martamusikmaschine/mmm/3d/led_ring.jpg

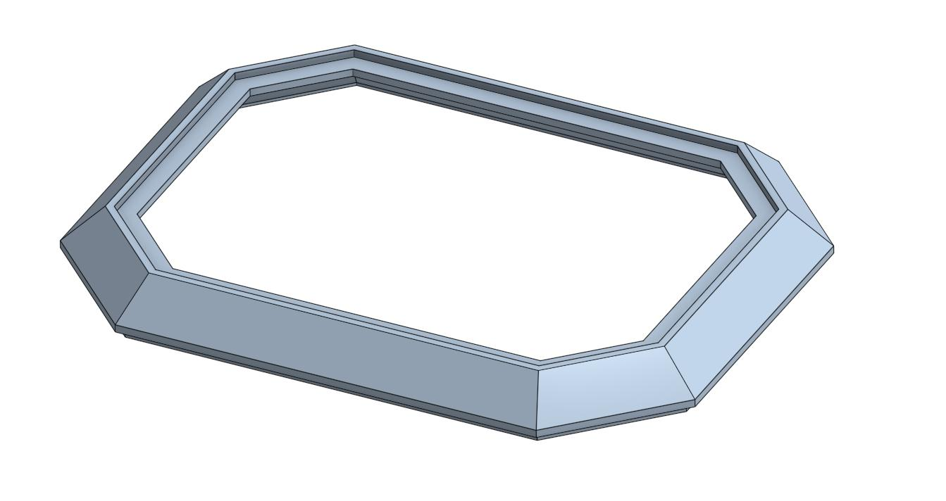
3d/led_ring.jpg
