martamusikmaschine/mmm/3d/rfid_reader_main.jpg

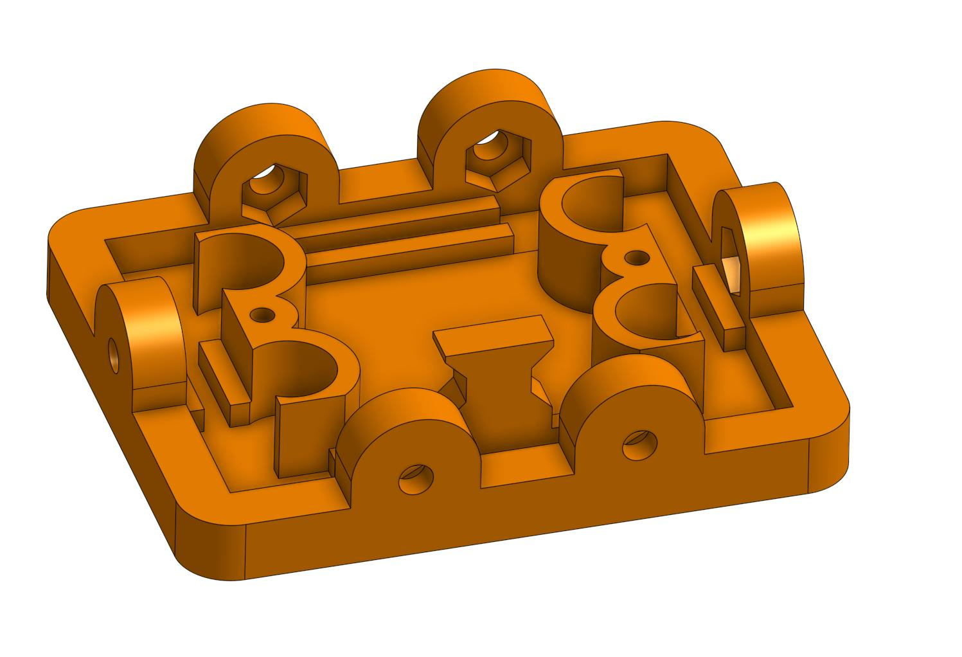
3d/rfid_reader_main.jpg
