martamusikmaschine/mmm/3d/rfid_tag_44_29_cap.jpg

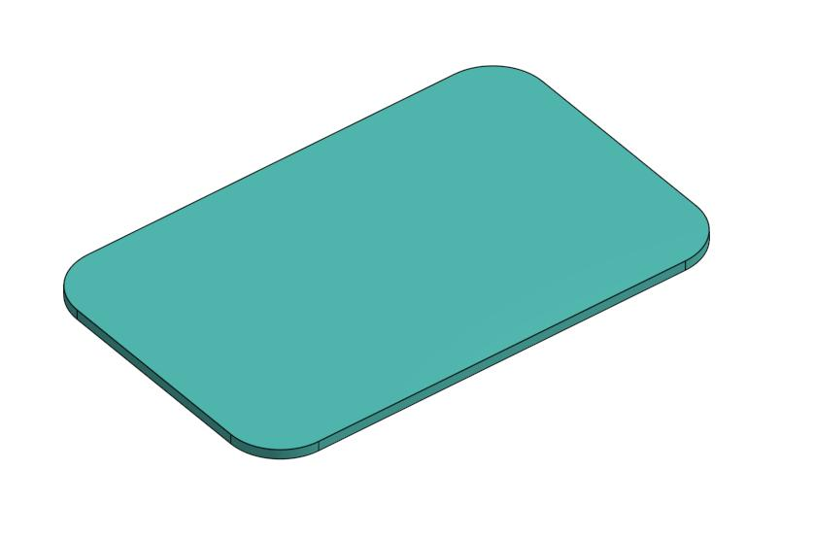
3d/rfid_tag_44_29_cap.jpg
