martamusikmaschine/mmm/3d/top_plate.jpg

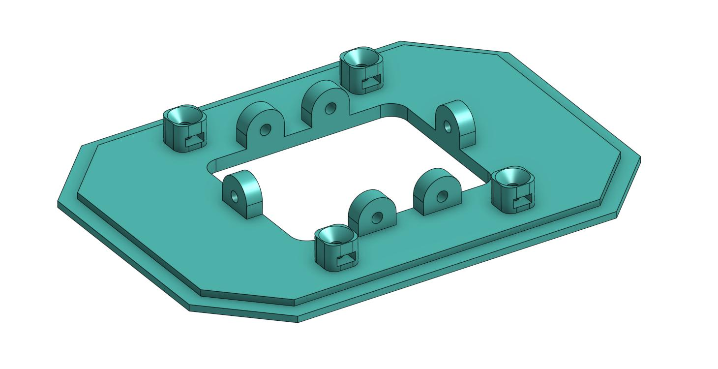
3d/top_plate.jpg
