martamusikmaschine/mmm/3d/rfid_tag_44_29_photo_holder.stl

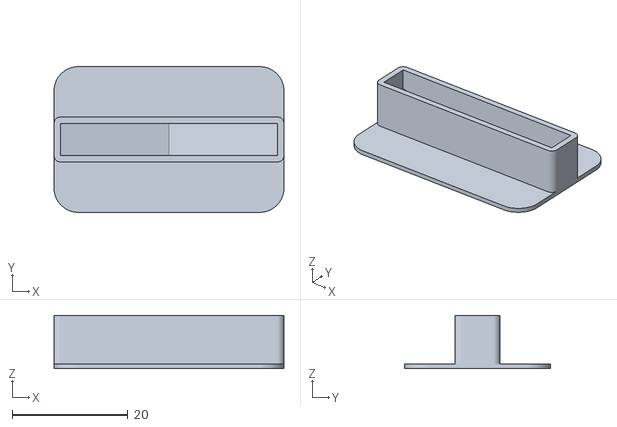
[picture p25: CAD file, 2019-08-26]
3d/rfid_tag_44_29_photo_holder.stl
39.8 x 25.2 x 9.20
