martamusikmaschine/mmm/3d/rfid_tag_50_30_base.stl

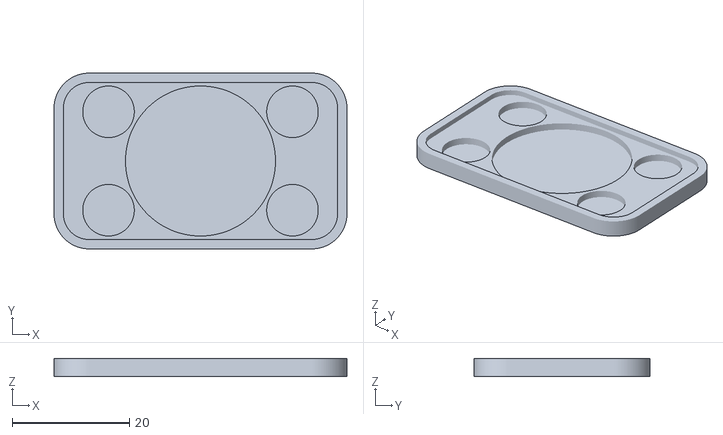
[picture p26: CAD file, 2019-08-26]
3d/rfid_tag_50_30_base.stl
50.0 x 30.0 x 3.10
