martamusikmaschine/mmm/3d/rfid_tag_80_30_cap.stl

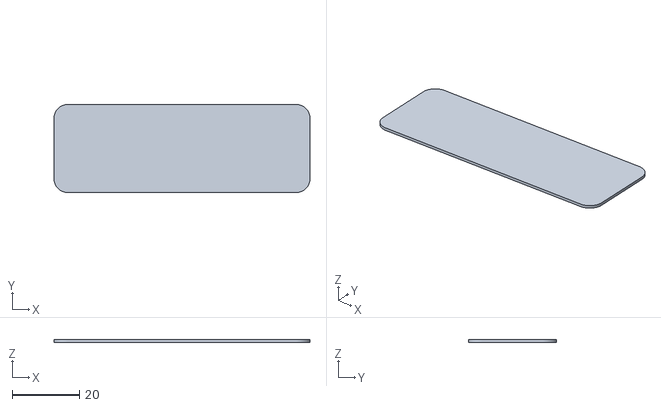
[picture p27: CAD file, 2019-08-26]
3d/rfid_tag_80_30_cap.stl
76.2 x 26.2 x 0.8
