martamusikmaschine/mmm/3d/rfid_tag_62_32_base.stl

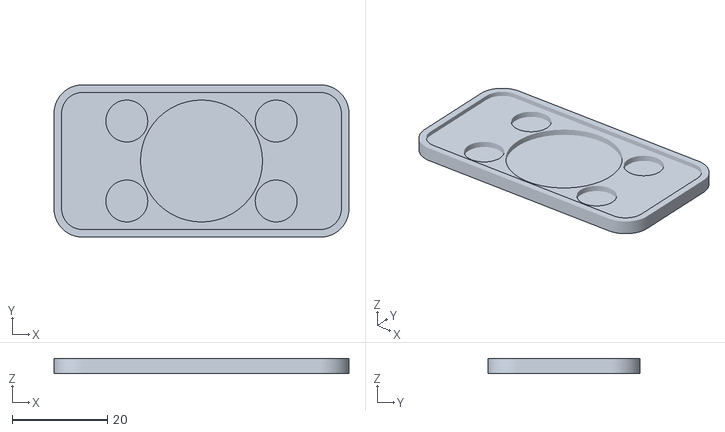
[picture p28: CAD file, 2019-08-26]
3d/rfid_tag_62_32_base.stl
62.0 x 32.0 x 3.10
