martamusikmaschine/mmm/3d/rfid_tag_50_30_cap.stl

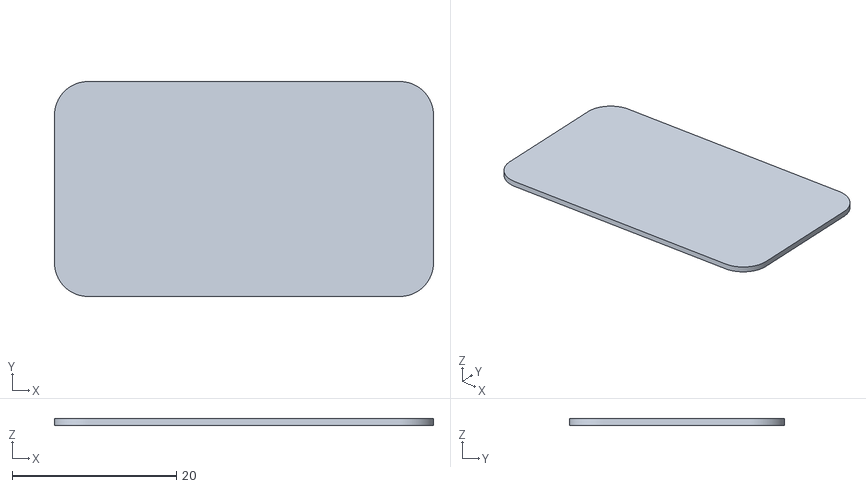
[picture p29: CAD file, 2019-08-26]
3d/rfid_tag_50_30_cap.stl
46.2 x 26.2 x 0.8
