martamusikmaschine/mmm/3d/rfid_tag_80_30_base.stl

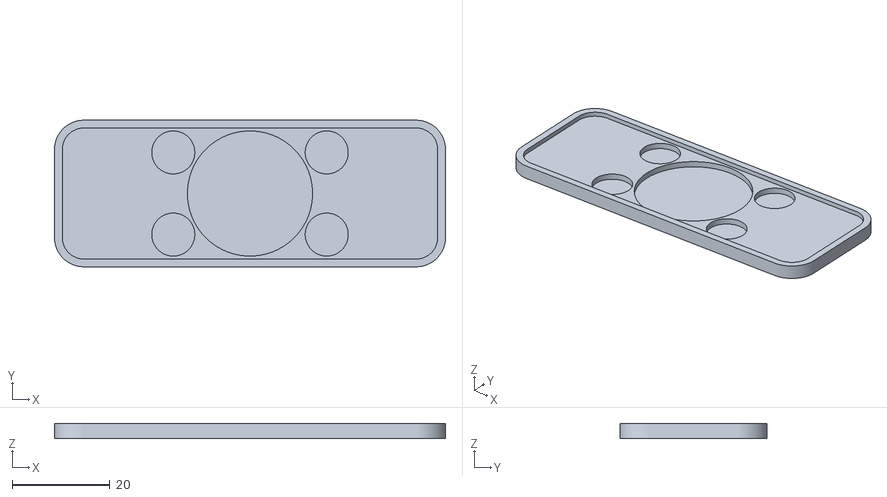
[picture p30: CAD file, 2019-08-26]
3d/rfid_tag_80_30_base.stl
80.0 x 30.0 x 3.10
