martamusikmaschine/mmm/3d/rfid_tag_62_32_cap.stl

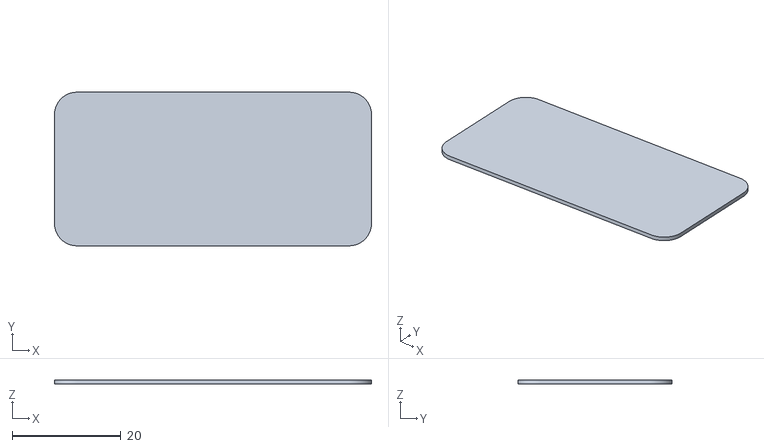
[picture p31: CAD file, 2019-08-26]
3d/rfid_tag_62_32_cap.stl
58.2 x 28.2 x 0.8
