martamusikmaschine/mmm/3d/rfid_tag_55_55_base.stl

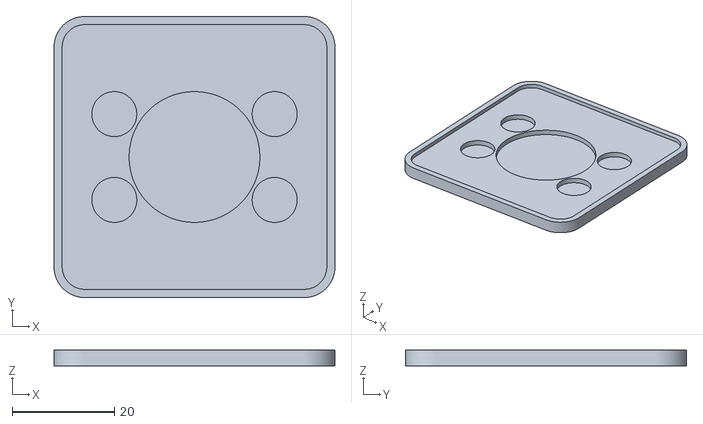
[picture p32: CAD file, 2019-08-26]
3d/rfid_tag_55_55_base.stl
55.0 x 55.0 x 3.10
