martamusikmaschine/mmm/3d/rfid_tag_44_35_cap.stl

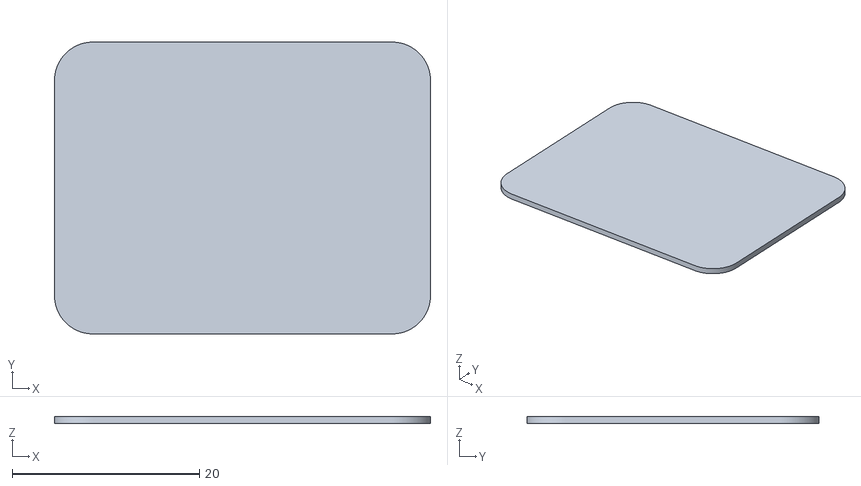
[picture p33: CAD file, 2019-08-26]
3d/rfid_tag_44_35_cap.stl
40.2 x 31.2 x 0.8
