martamusikmaschine/mmm/3d/rfid_tag_50_50_cap.stl

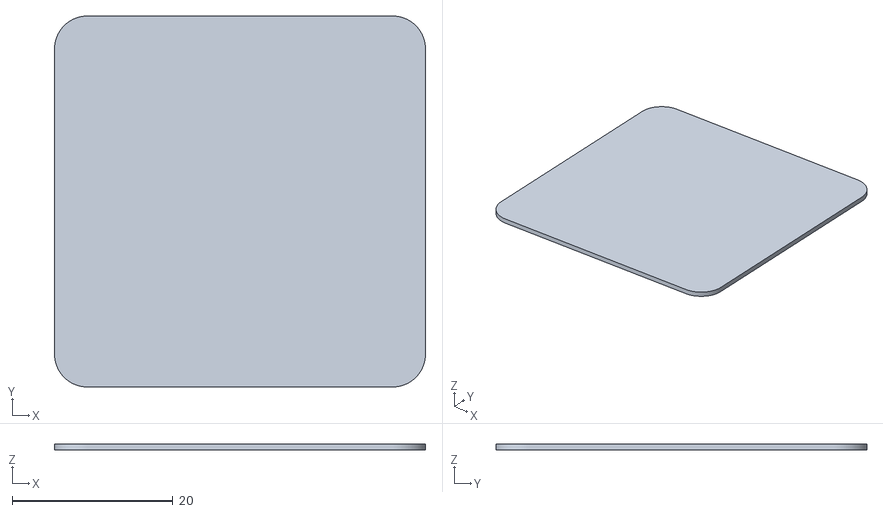
[picture p34: CAD file, 2019-08-26]
3d/rfid_tag_50_50_cap.stl
46.2 x 46.2 x 0.8
