martamusikmaschine/mmm/3d/rfid_tag_50_35_base.stl

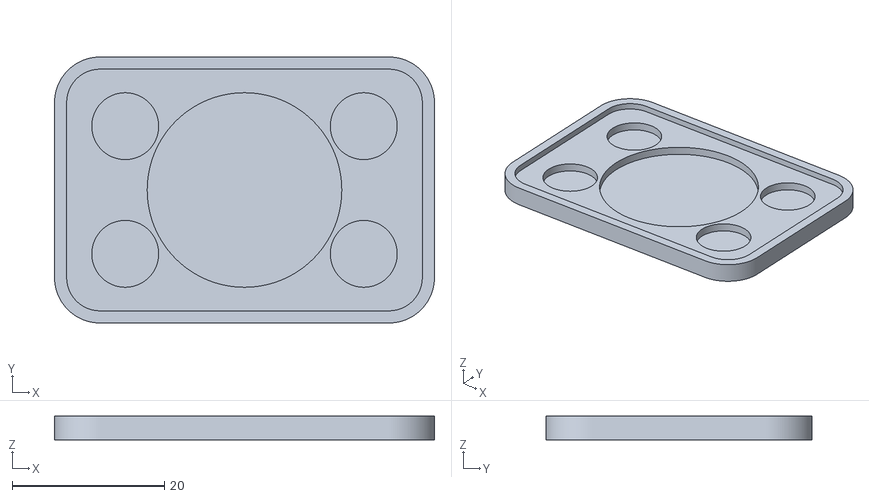
[picture p35: CAD file, 2019-08-26]
3d/rfid_tag_50_35_base.stl
50.0 x 35.0 x 3.10
