martamusikmaschine/mmm/3d/rfid_tag_80_60_cap.stl

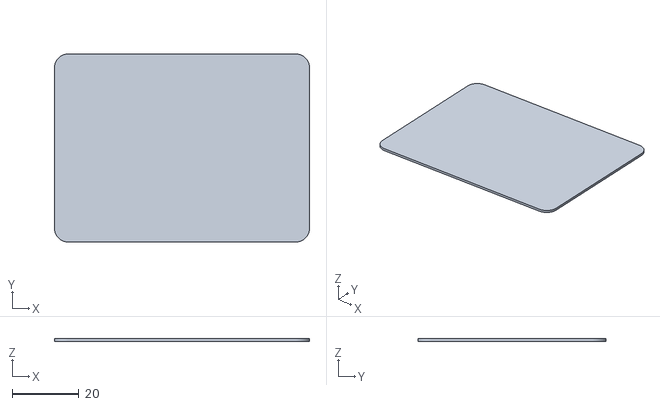
[picture p36: CAD file, 2019-08-26]
3d/rfid_tag_80_60_cap.stl
76.2 x 56.2 x 0.8
