martamusikmaschine/mmm/3d/rfid_tag_50_35_cap.stl

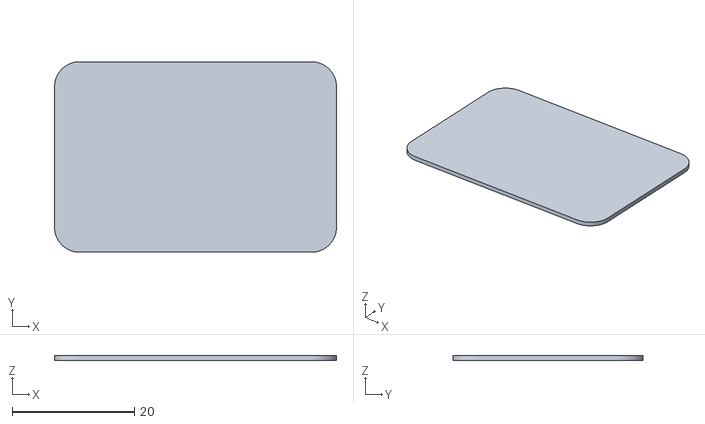
[picture p37: CAD file, 2019-08-26]
3d/rfid_tag_50_35_cap.stl
46.2 x 31.2 x 0.8
