martamusikmaschine/mmm/3d/rfid_tag_55_30_cap.stl

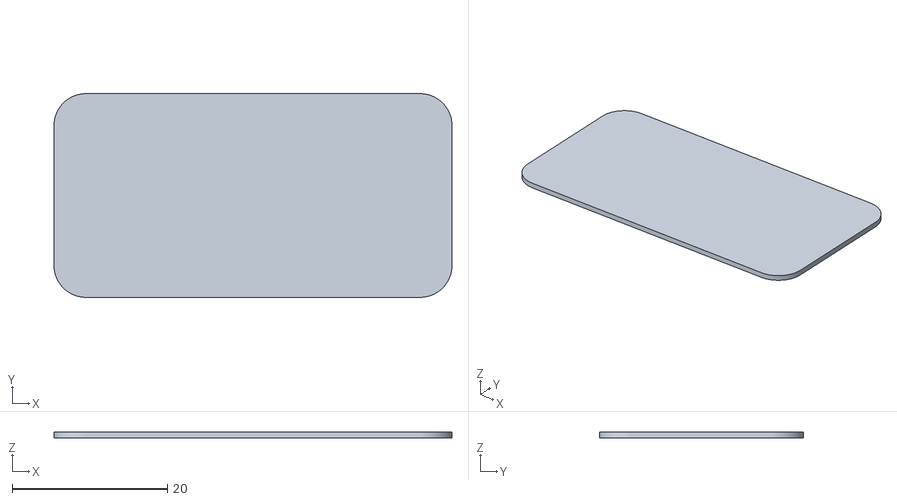
[picture p38: CAD file, 2019-08-26]
3d/rfid_tag_55_30_cap.stl
51.2 x 26.2 x 0.8
