martamusikmaschine/mmm/3d/rfid_tag_50_50_base.stl

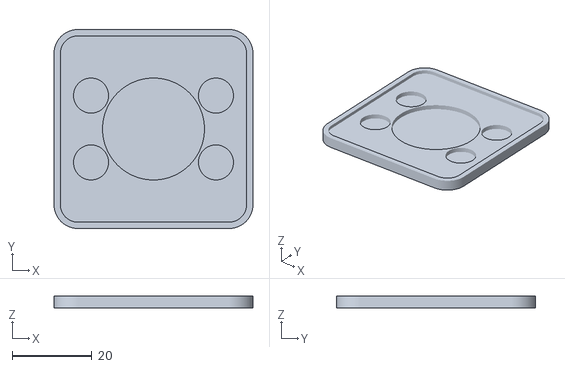
[picture p39: CAD file, 2019-08-26]
3d/rfid_tag_50_50_base.stl
50.0 x 50.0 x 3.10
