martamusikmaschine/mmm/3d/rfid_tag_60_35_base.stl

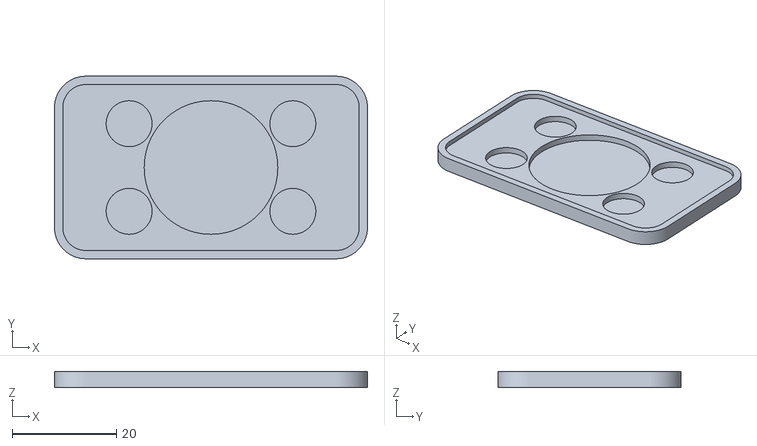
[picture p40: CAD file, 2019-08-26]
3d/rfid_tag_60_35_base.stl
60.0 x 35.0 x 3.10
