martamusikmaschine/mmm/marta/MartaHandler.py

class MartaHandler(object):
    EVENT_HANDLER_DONE = -1

    def __init__(self, marta):
        self.marta = marta

    def initialize(self):
        pass

    def uninitialize(self):
        pass

    def rfid_tag_event(self, tag):
        return

    def rotation_event(self, x, y):
        return

    def player_stop_event(self):
        return

    def button_event(self, pin, millis):
        return
