martamusikmaschine/mmm/marta/Util.py

import re


# thanks https://stackoverflow.com/a/48030307
def sorted_aphanumeric(data):
    convert = lambda text: int(text) if text.isdigit() else text.lower()
    alphanum_key = lambda key: [convert(c) for c in re.split('([0-9]+)', key)]
    return sorted(data, key=alphanum_key)
